johnyHV/PIR_LED_STRIP/docu/1.jpg

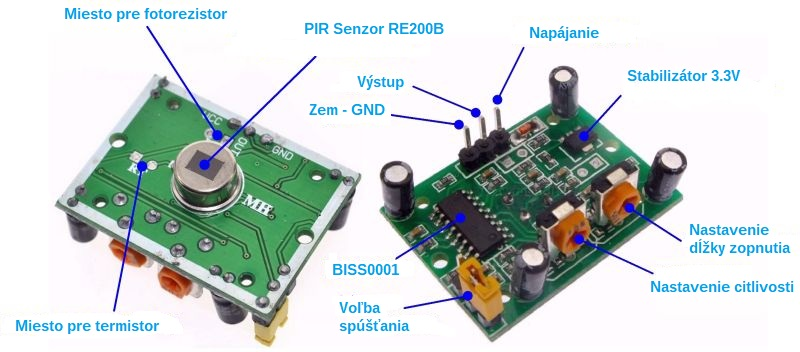
docu/1.jpg
