johnyHV/PIR_LED_STRIP/docu/4.jpg

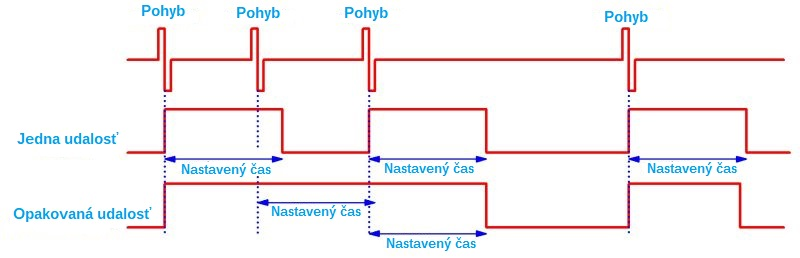
docu/4.jpg
