johnyHV/PIR_LED_STRIP/docu/add_lib_1.png

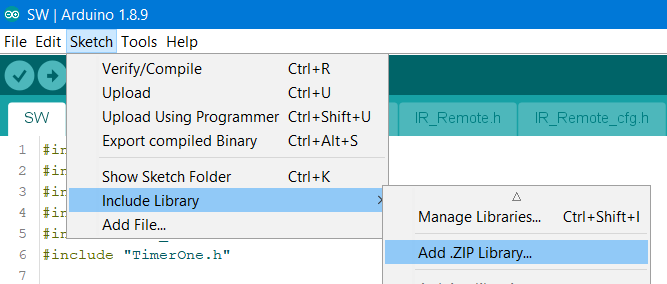
docu/add_lib_1.png
