johnyHV/PIR_LED_STRIP/docu/add_lib_2.png

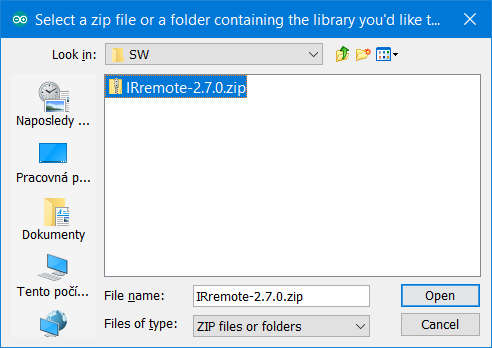
docu/add_lib_2.png
