johnyHV/PIR_LED_STRIP/docu/add_lib_3.png

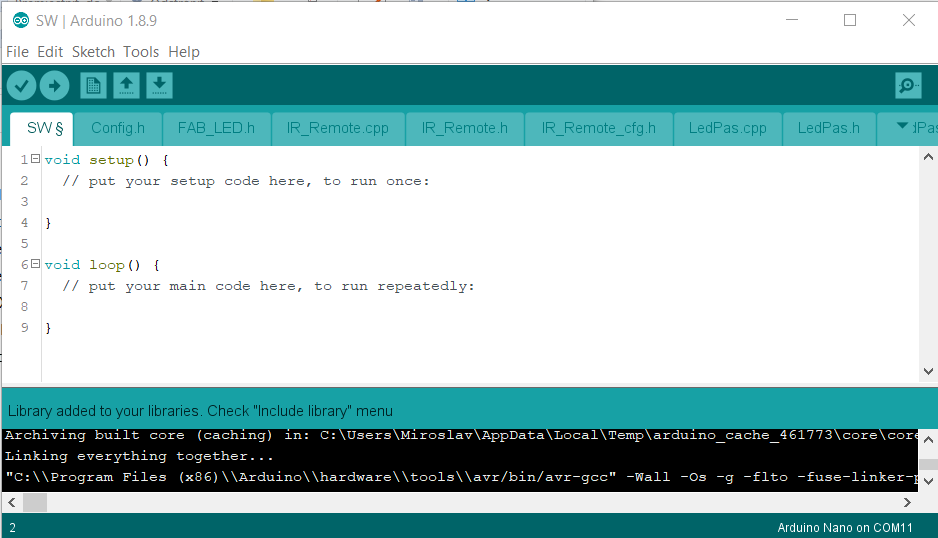
docu/add_lib_3.png
