johnyHV/PIR_LED_STRIP/docu/DSCF5875_EDIT.jpg

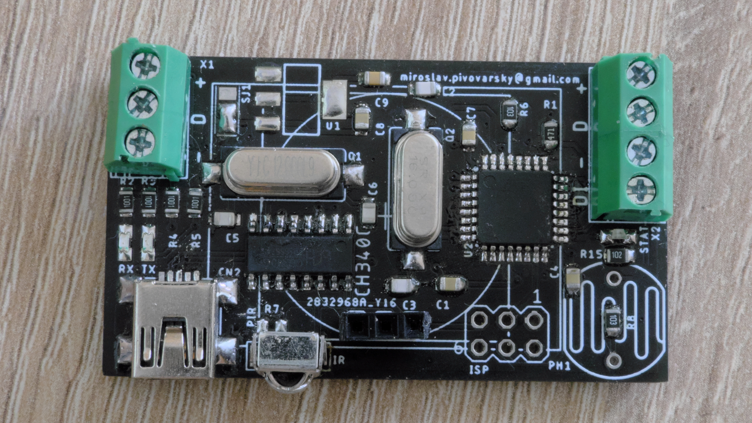
docu/DSCF5875_EDIT.jpg
