johnyHV/PIR_LED_STRIP/docu/DSCF5877_EDIT.jpg

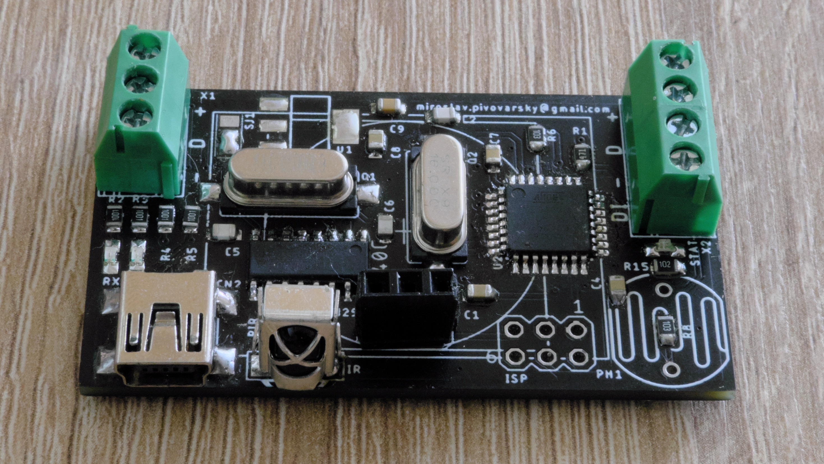
docu/DSCF5877_EDIT.jpg
