johnyHV/PIR_LED_STRIP/docu/ezgif.com-webp-to-jpg (1).jpg

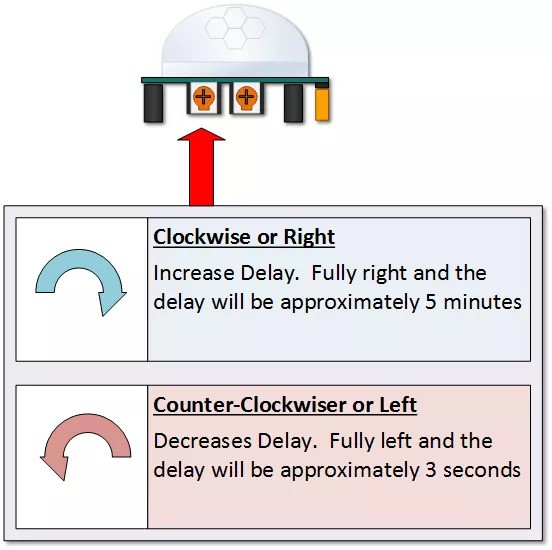
docu/ezgif.com-webp-to-jpg (1).jpg
