johnyHV/PIR_LED_STRIP/docu/ezgif.com-webp-to-jpg.jpg

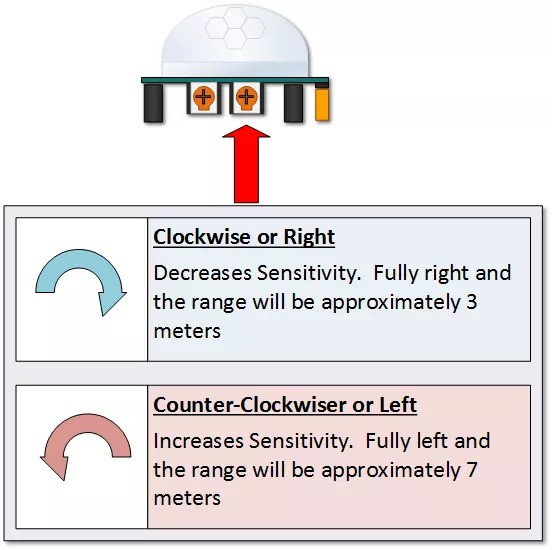
docu/ezgif.com-webp-to-jpg.jpg
