johnyHV/PIR_LED_STRIP/docu/konstrukcia/CORNER10/hlinikovy-profil-pre-led-pasy-corner (1).jpg

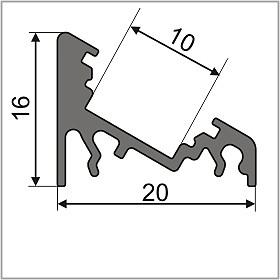
docu/konstrukcia/CORNER10/hlinikovy-profil-pre-led-pasy-corner (1).jpg
