johnyHV/PIR_LED_STRIP/docu/konstrukcia/CORNER10/hlinikovy-profil-pre-led-pasy-corner-a.jpg

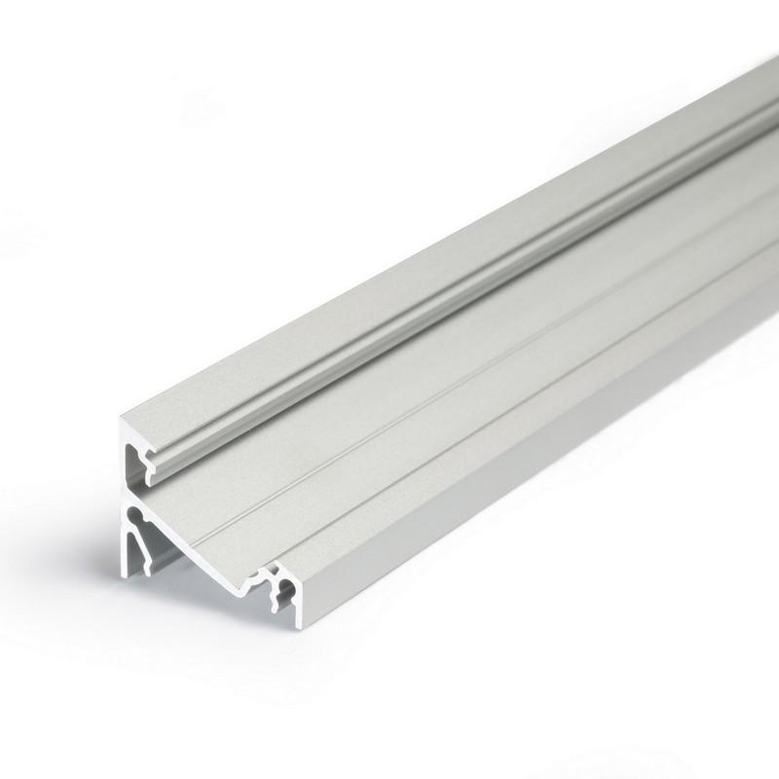
docu/konstrukcia/CORNER10/hlinikovy-profil-pre-led-pasy-corner-a.jpg
