johnyHV/PIR_LED_STRIP/docu/konstrukcia/CORNER10/prava-krytka-pre-profil-corner.jpg

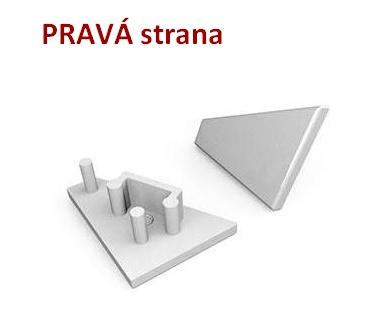
docu/konstrukcia/CORNER10/prava-krytka-pre-profil-corner.jpg
