johnyHV/PIR_LED_STRIP/docu/konstrukcia/CORNER10/spojka-na-profily-groove-corner-surface.jpg

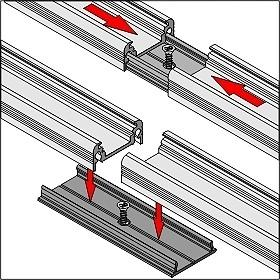
docu/konstrukcia/CORNER10/spojka-na-profily-groove-corner-surface.jpg
