johnyHV/PIR_LED_STRIP/docu/konstrukcia/CORNER10/spojka-x.jpg

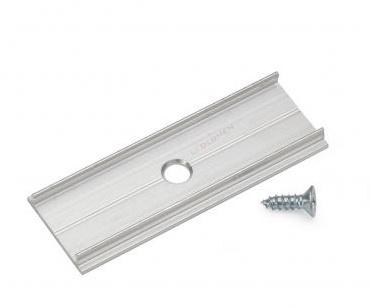
docu/konstrukcia/CORNER10/spojka-x.jpg
