johnyHV/PIR_LED_STRIP/docu/konstrukcia/MICRO-ALU/6251-2.png

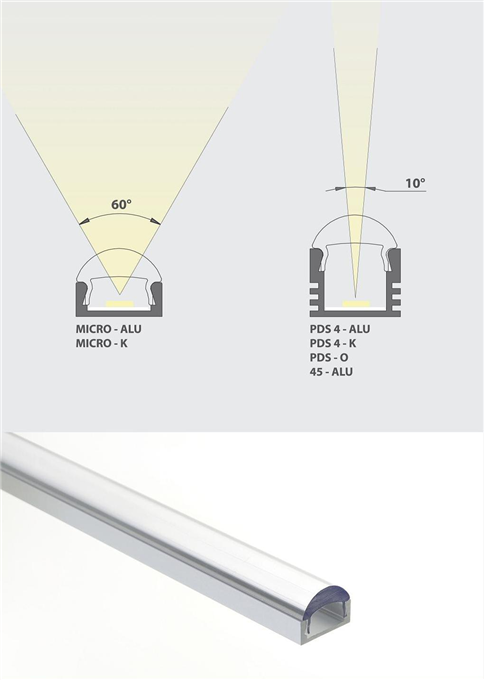
docu/konstrukcia/MICRO-ALU/6251-2.png
