johnyHV/PIR_LED_STRIP/docu/konstrukcia/MICRO-ALU/19176_21431-bf50b53ef2-jpg_1.jpg

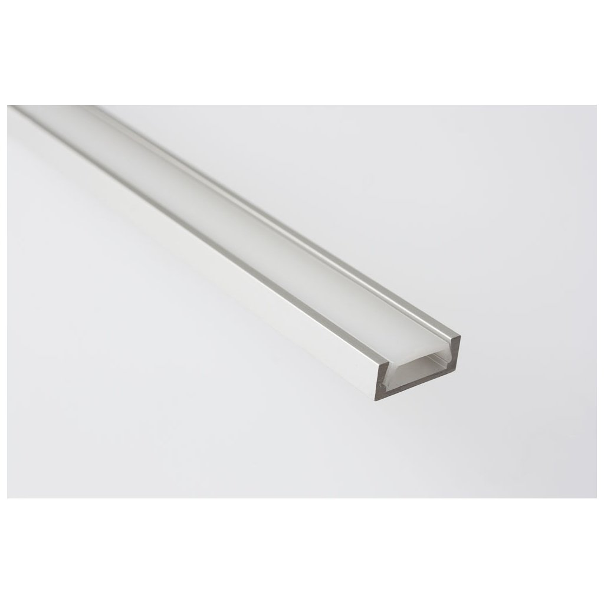
docu/konstrukcia/MICRO-ALU/19176_21431-bf50b53ef2-jpg_1.jpg
