johnyHV/PIR_LED_STRIP/docu/konstrukcia/MICRO-ALU/22408_6017-540a89d7b4-jpg_1.jpg

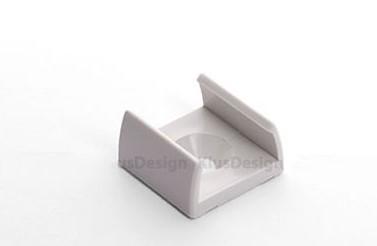
docu/konstrukcia/MICRO-ALU/22408_6017-540a89d7b4-jpg_1.jpg
