johnyHV/PIR_LED_STRIP/docu/konstrukcia/MICRO-ALU/img.jpg

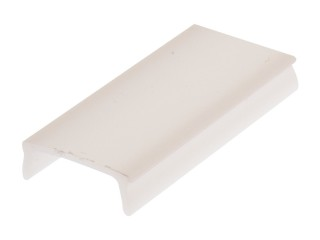
docu/konstrukcia/MICRO-ALU/img.jpg
