johnyHV/PIR_LED_STRIP/docu/LED.png

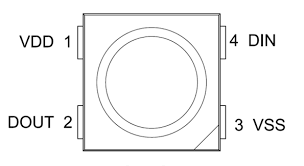
docu/LED.png
