johnyHV/PIR_LED_STRIP/docu/P_20201011_174345.jpg

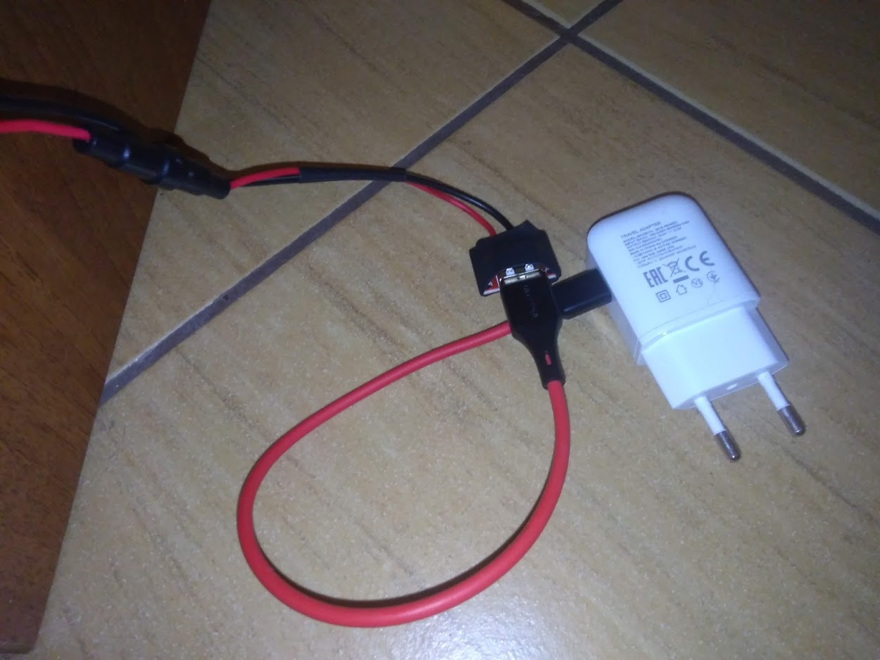
docu/P_20201011_174345.jpg
