johnyHV/PIR_LED_STRIP/docu/PIR graf.jpg

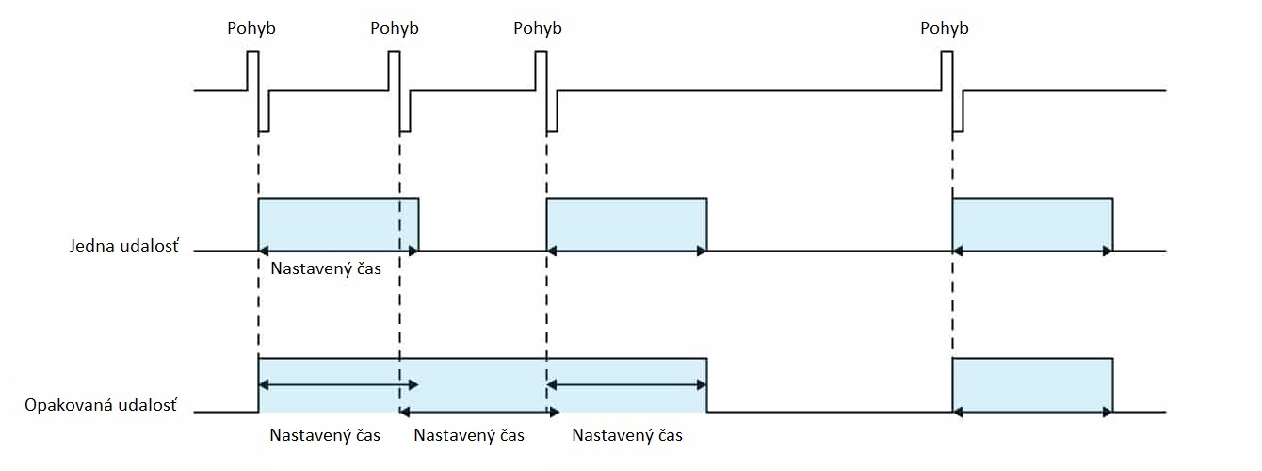
docu/PIR graf.jpg
