johnyHV/PIR_LED_STRIP/docu/PIR Senzor.jpg

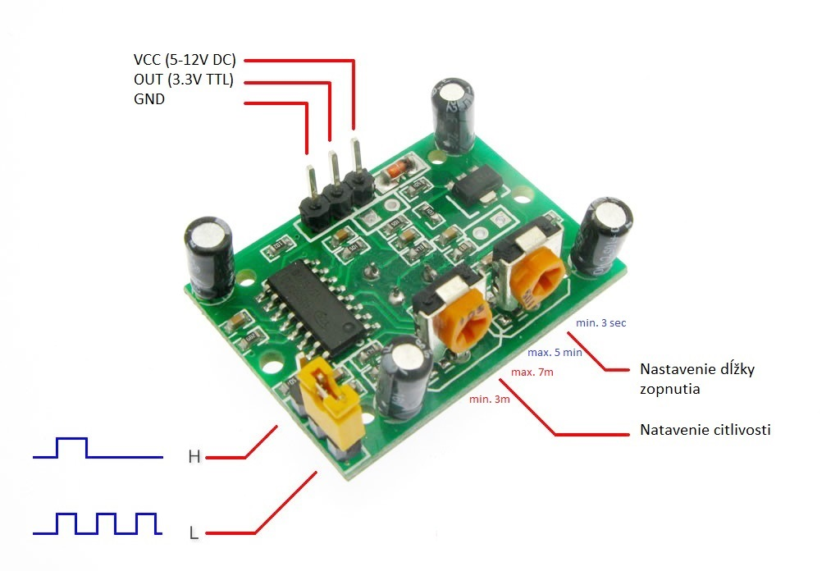
docu/PIR Senzor.jpg
