johnyHV/PIR_LED_STRIP/docu/PIR_LedStrip v1.0_TOP.png

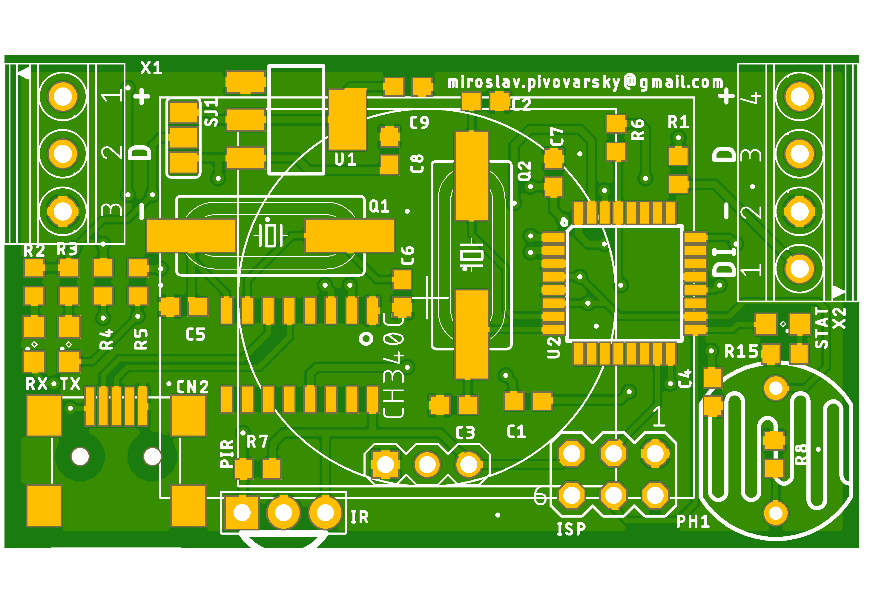
docu/PIR_LedStrip v1.0_TOP.png
