johnyHV/PIR_LED_STRIP/docu/s-l300.jpg

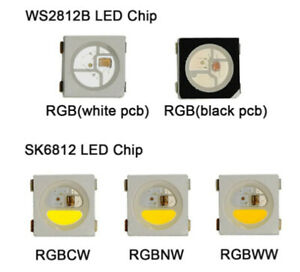
docu/s-l300.jpg
