johnyHV/PIR_LED_STRIP/docu/x1kidqi_grobo.jpg

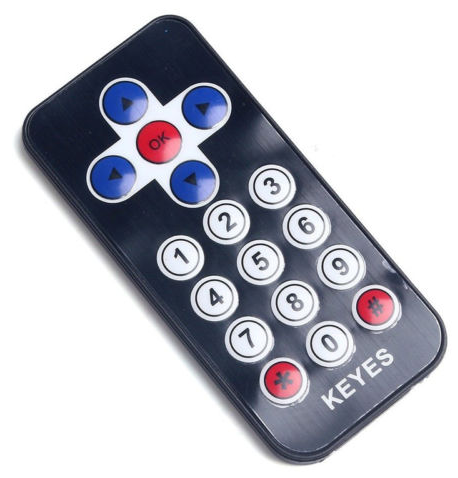
docu/x1kidqi_grobo.jpg
