johnyHV/PIR_LED_STRIP/docu/zapojenie.png

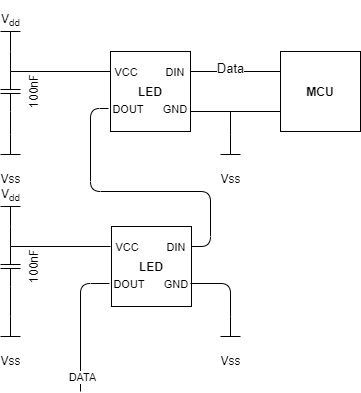
docu/zapojenie.png
