johnyHV/PIR_LED_STRIP/docu/Zapojenie_blok.png

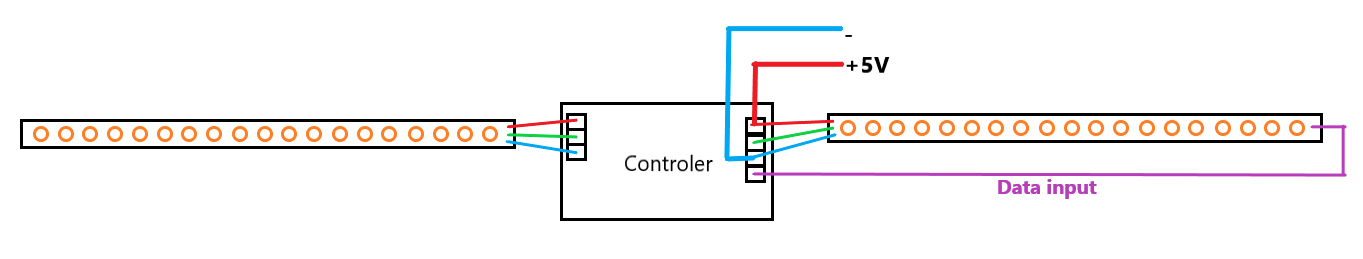
docu/Zapojenie_blok.png
