johnyHV/PIR_LED_STRIP/SW/IR_Remote_cfg.h

/**
   @file IR_Remote_cfg.h

   @brief Konfiguracia kniznice pre pracu s IR dialkovym ovladanim

   @author Miroslav Pivovarsky
   Contact: miroslav.pivovarsky@gmail.com

   @bug: no know bug

*/

#ifndef _REMOTE_CFG_H_
#define _REMOTE_CFG_H_

#define IR_REMOTE_ENABLE true                   ///< Zapnutie/vypnutie podpory IRremote kniznice v kompilacnom procese

#define IR_REMOTE_BUTTON_0        0xFF4AB5      ///< Tlacidlo 0
#define IR_REMOTE_BUTTON_1        0xFF6897      ///< Tlacidlo 1
#define IR_REMOTE_BUTTON_2        0xFF9867      ///< Tlacidlo 2
#define IR_REMOTE_BUTTON_3        0xFFB04F      ///< Tlacidlo 3
#define IR_REMOTE_BUTTON_4        0xFF30CF      ///< Tlacidlo 4
#define IR_REMOTE_BUTTON_5        0xFF18E7      ///< Tlacidlo 5
#define IR_REMOTE_BUTTON_6        0xFF7A85      ///< Tlacidlo 6
#define IR_REMOTE_BUTTON_7        0xFF10EF      ///< Tlacidlo 7
#define IR_REMOTE_BUTTON_8        0xFF38C7      ///< Tlacidlo 8
#define IR_REMOTE_BUTTON_9        0xFF5AA5      ///< Tlacidlo 9
#define IR_REMOTE_BUTTON_HASHTAG  0xFF42BD      ///< Tlacidlo #
#define IR_REMOTE_BUTTON_STAR     0xFF52AD      ///< Tlacidlo *

#endif

/* EOF */
